nnovofastovskiy/violetMonitor/datasheets/141_4.jpg

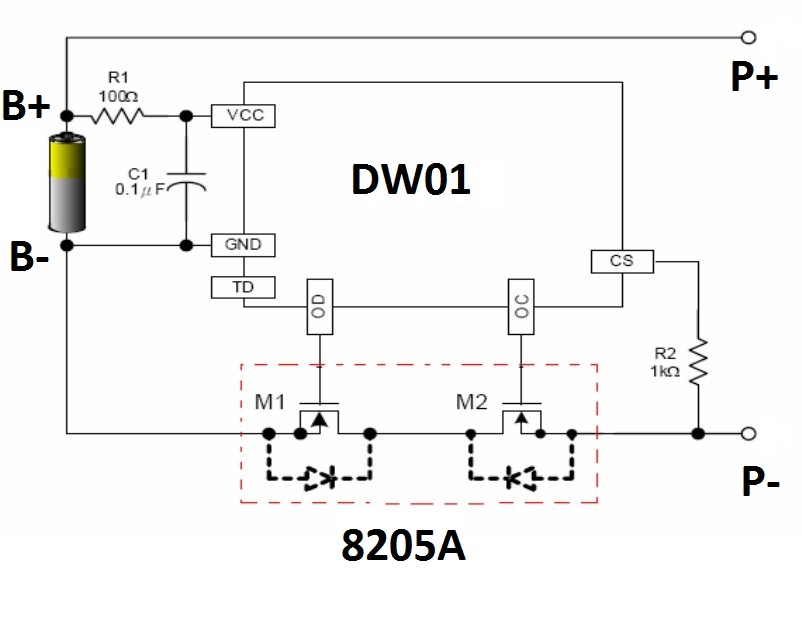
datasheets/141_4.jpg
