nnovofastovskiy/violetMonitor/schematic/other/Assembly v8.step

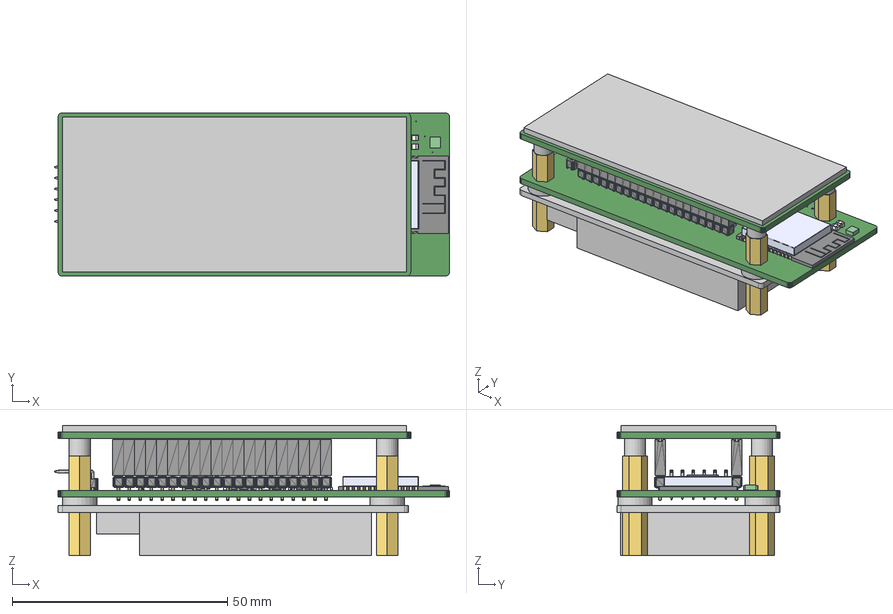
[picture p21: CAD file, 2025-02-13, an earlier design]
schematic/other/Assembly v8.step
91.8 x 38.0 x 30.3 mm
PCHSN-8 x 4
Board___wctmp
PBS_20 x 2
Board___wctmp_1
GRM21BR61A106KE19B x 5
GRM32ER71E226KE15L
GRM155R61C105KA12D x 4
TECAP2.2/16VA10
t_mod_0
t_mod_0 (1)
BSS138LT1G
BC817-16,235 x 2
RC0402FR-071K2L x 7
RC0805JR-0710KL x 5
ETA9640
t_mod_1
pls_20 x 2
pls_6R
LP103450 battery
Plane
PCHSN-10 v1 x 4
